insolace/ColorSynth/IMG/CS1.jpg

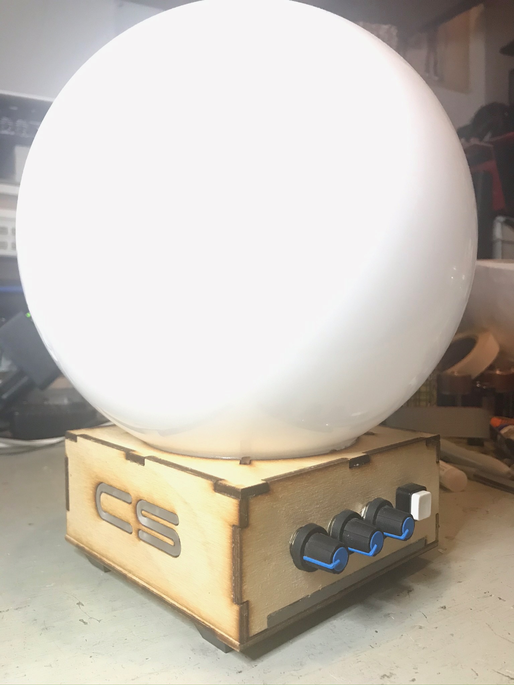
IMG/CS1.jpg
