insolace/ColorSynth/IMG/CS2.jpg

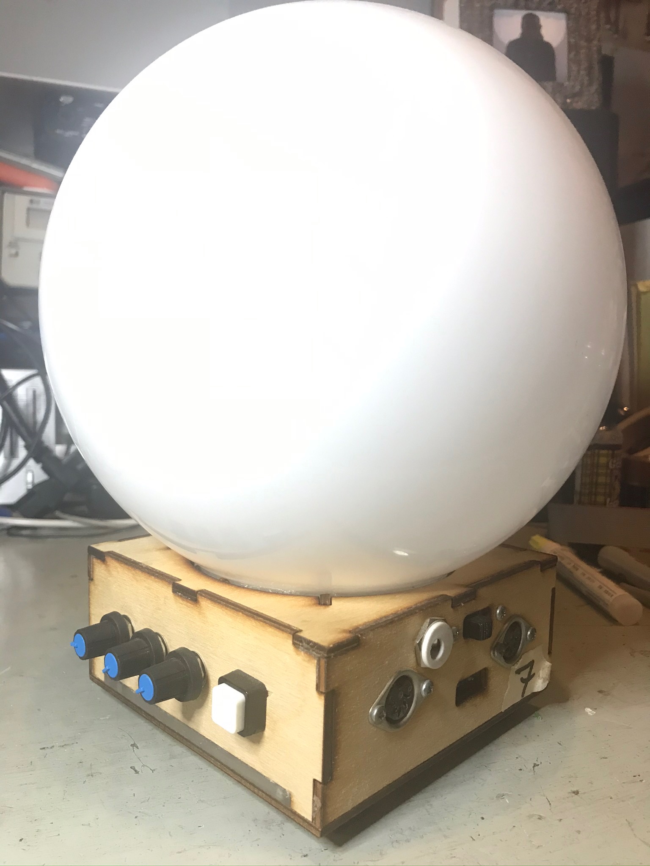
IMG/CS2.jpg
