insolace/ColorSynth/IMG/CS Blue.jpg

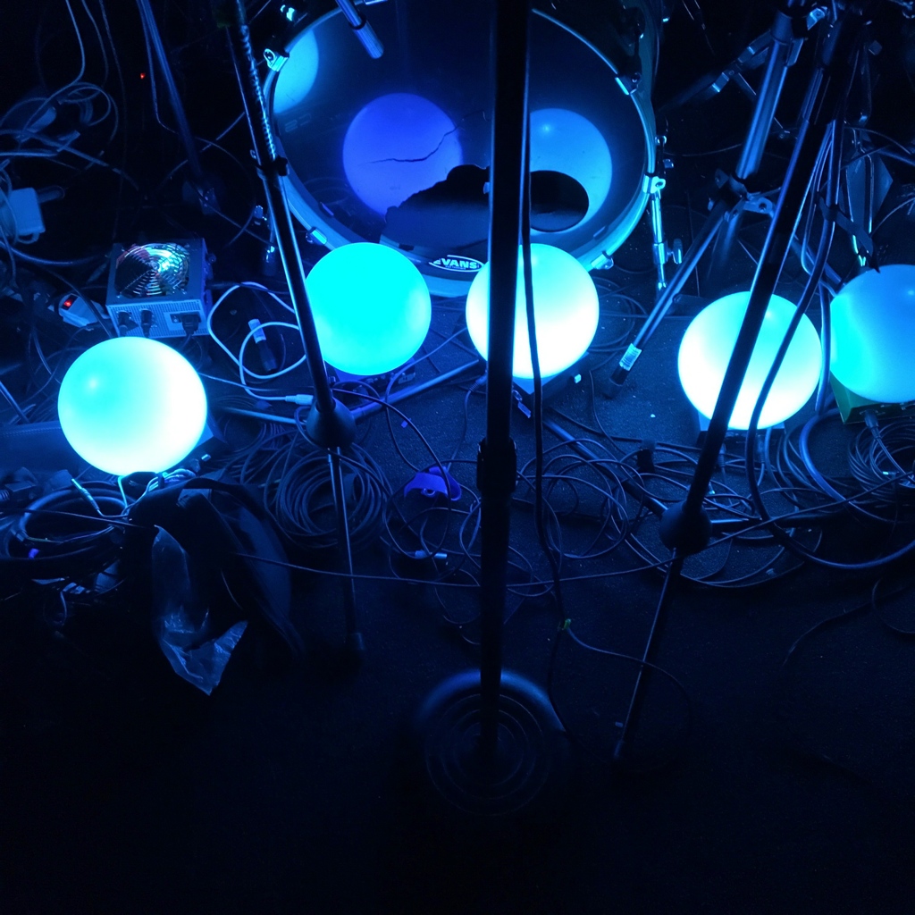
IMG/CS Blue.jpg
