insolace/ColorSynth/IMG/CS-ASM.png

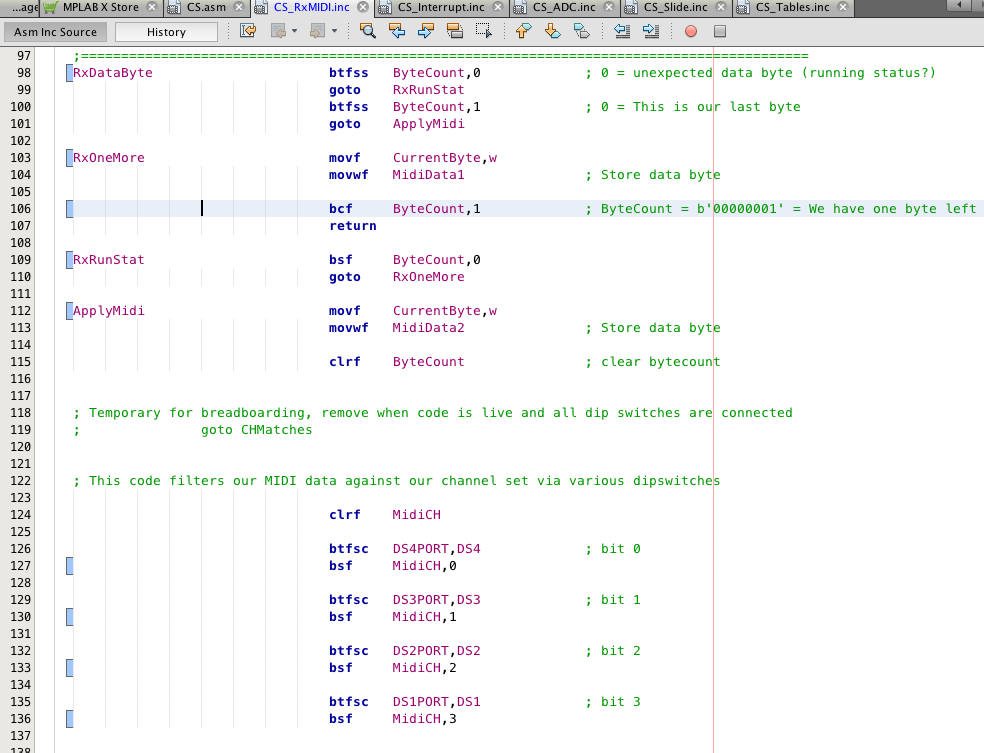
IMG/CS-ASM.png
