insolace/ColorSynth/IMG/CS-fixture.png

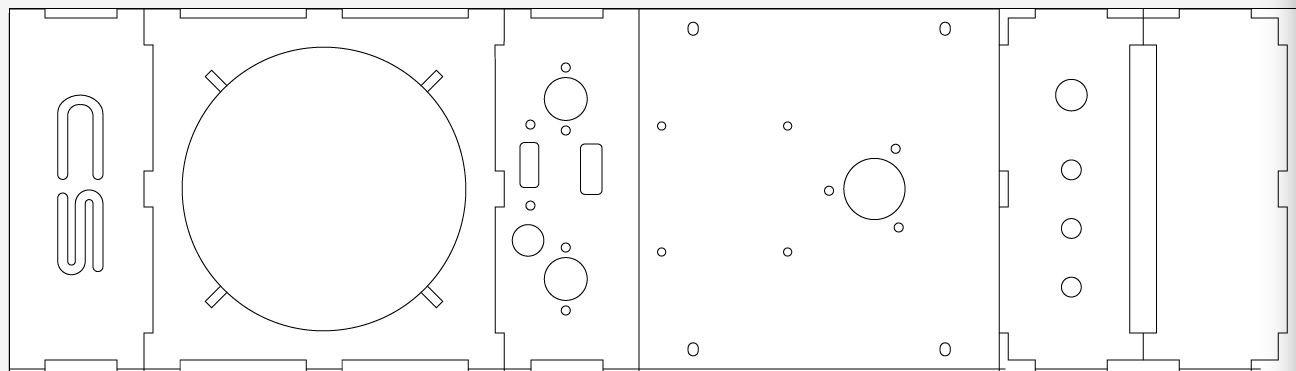
IMG/CS-fixture.png
