insolace/ColorSynth/IMG/H - Final.JPG

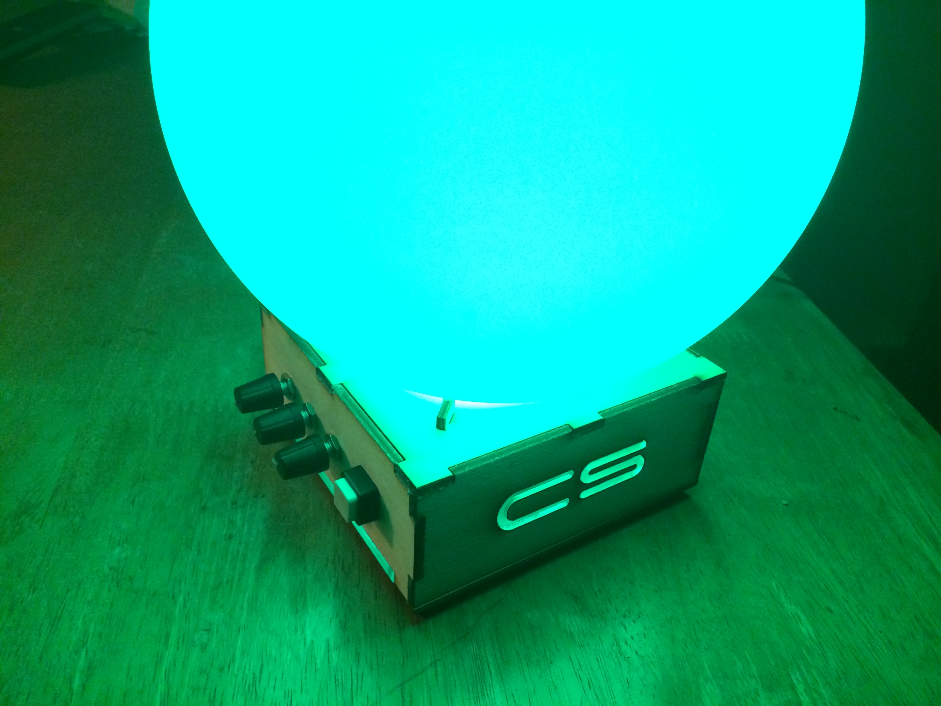
IMG/H - Final.JPG
