insolace/ColorSynth/IMG/I - CS-anim.gif

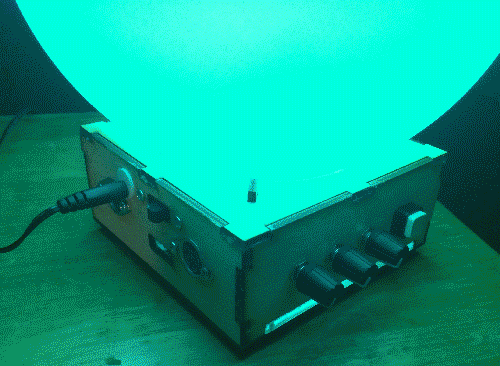
IMG/I - CS-anim.gif
