insolace/ColorSynth/PCB and Schematic/PCB Render/CS-PCB-V2.0-components.jpg

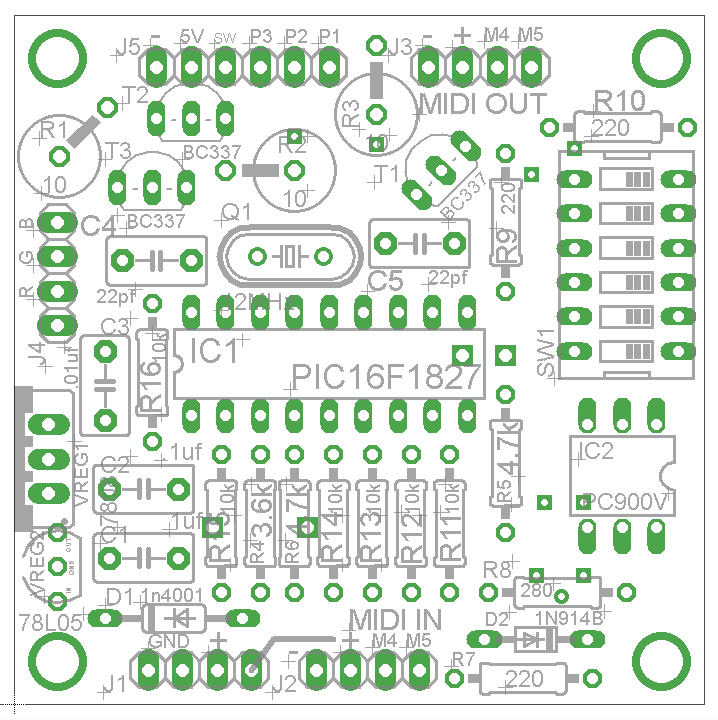
PCB and Schematic/PCB Render/CS-PCB-V2.0-components.jpg
